Demitha-Manawadu/Robotic-Design-Project/car_code_new/car_codebase/AdvancedMotorControl.cpp

#include "AdvancedMotorControl.h"
#include "MotorControl.h"
#include "SensorControl.h"
#include <Arduino.h>
#include "OLED_Display.h"
#include "task2.h"
// PID control variables for forward motion
float forwardKp = .95;  // Proportional gain try using 3500/180
float forwardKi = 0.0;  // Integral gain
float forwardKd = .55;    // Derivative gain
float forwardLastError = 0;
float forwardIntegral = 0;

// PID control variables for backward motion
float backwardKp = .5;  // Proportional gain
float backwardKi = 0.00;  // Integral gain
float backwardKd = 0.4;  // Derivative gain
float backwardLastError = 0;
float backwardIntegral = 0;

//int pathcolor=0;
// Function to run forward using PID of the sensor array (without time constraint)
void runForwardWithSensorPID() {
  Serial.println("Running Forward with Sensor Array PID...");

   // Infinite loop to keep running until some external condition breaks the loop
    // Read and normalize sensor values
    readSensors();

    // Calculate the position value using a weighted sum
    int position = calculatePosition();
    int error;
    //pathcolor=0;
    // Compute the error
    // if (pathcolor==1){
    // error = position - 3500;
    // }
    // else{error = position;}  // Assume line center at 3500
    error = position;

    // Compute the PID control values
    forwardIntegral += error;
    float derivative = error - forwardLastError;
    float output = forwardKp * error + forwardKi * forwardIntegral + forwardKd * derivative;
    forwardLastError = error;

    // Adjust the motor speeds based on the PID output
    int baseSpeed = 170;
    int leftSpeed = baseSpeed - output;
    int rightSpeed = baseSpeed + output;

    // Ensure motor speeds are within a valid range
    leftSpeed = constrain(leftSpeed, 0, 255);
    rightSpeed = constrain(rightSpeed, 0, 255);

    // Move the car forward with the calculated speeds
    moveForward(leftSpeed, rightSpeed);
    delay(20);
    // You can add a break condition here if needed
    // Example: if (someConditionMet) { break; }
}

// Function to run backward using PID of the encoders (without time constraint)
void runBackwardWithEncoderPID() {
  // Reset encoder counts before moving backward
  leftEncoderCount = 0;
  rightEncoderCount = 0;

  Serial.println("Running Backward with Encoder PID...");

  while (true) {  // Infinite loop to keep running until some external condition breaks the loop
    // Calculate the error using encoder counts
    long error = leftEncoderCount - rightEncoderCount;

    // Compute the PID control values
    backwardIntegral += error;
    float derivative = error - backwardLastError;
    float output = backwardKp * error + backwardKi * backwardIntegral + backwardKd * derivative;
    backwardLastError = error;

    // Adjust the motor speeds based on the PID output
    int baseSpeed = 180;
    int leftSpeed = baseSpeed - output;
    int rightSpeed = baseSpeed + output;

    // Ensure motor speeds are within a valid range
    leftSpeed = constrain(leftSpeed, 0, 255);
    rightSpeed = constrain(rightSpeed, 0, 255);

    // Move the car backward with the calculated speeds
    moveBackward(leftSpeed, rightSpeed);

    // You can add a break condition here if needed
    // Example: if (someConditionMet) { break; }
  }

  // Stop the motors after backward motion
  moveBackward(0, 0);
}

void runForwardWithEncoderPID(int targetSpeed) {
    leftEncoderCount = 0;
    rightEncoderCount = 0;

    // Reset PID control variables for forward motion
    forwardIntegral = 0;
    forwardLastError = 0;

    while (true) {
        long leftError = leftEncoderCount;    // Left encoder count
        long rightError = rightEncoderCount;  // Right encoder count
        
        // Calculate the error based on the difference between encoders
        long error = leftError - rightError;

        // Compute the PID control values
        forwardIntegral += error;  // Accumulate the error
        float derivative = error - forwardLastError;  // Change in error
        float output = (forwardKp * error) + (forwardKi * forwardIntegral) + (forwardKd * derivative);
        forwardLastError = error;  // Update last error

        // Calculate left and right speeds based on the PID output
        int leftSpeed = targetSpeed - output;  // Subtract output for left motor
        int rightSpeed = targetSpeed + output; // Add output for right motor

        // Ensure motor speeds are within a valid range
        leftSpeed = constrain(leftSpeed, 0, 255);
        rightSpeed = constrain(rightSpeed, 0, 255);

        // Move the car forward with the calculated speeds
        moveForward(leftSpeed, rightSpeed);

        // Optionally, add a break condition to stop the loop when desired
        // Example: if (someConditionMet) { break; }
    }

    moveForward(0, 0);  // Stop motors after forward motion
}
