Demitha-Manawadu/Robotic-Design-Project/car_code_new/car_codebase/MovementControl.h

#ifndef MOVEMENTCONTROL_H
#define MOVEMENTCONTROL_H


// Function to run forward for given encoder counts without PID (fixed speed of 180)
void runForwardWithoutPID(long targetCount);


// Function to run backward for given encoder counts without PID (fixed speed of 180)
void runBackwardWithoutPID(long targetCount);

#endif
